boehmec/BLE_NeoPixel_ControlBox/img/DSC_0704.JPG

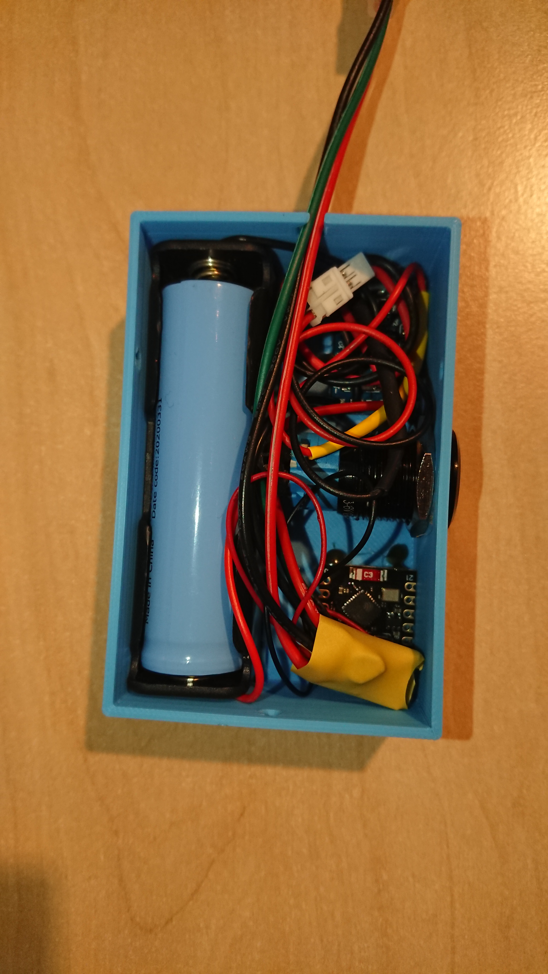
img/DSC_0704.JPG
