boehmec/BLE_NeoPixel_ControlBox/img/DSC_0705.JPG

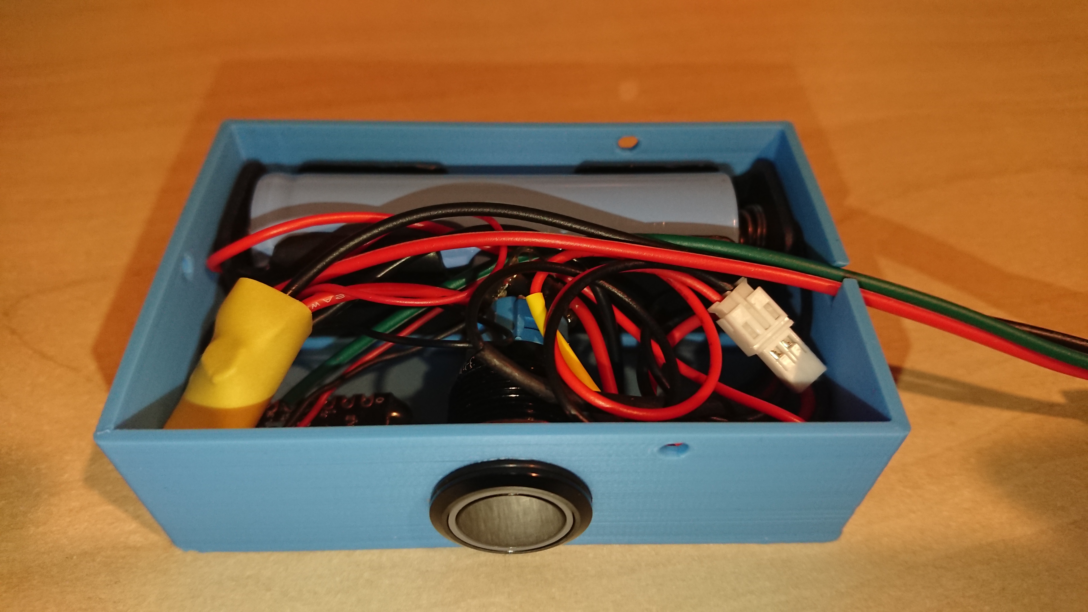
img/DSC_0705.JPG
